liysy020/Automation_Temperature_Station/ESP32/Source Python/upload.py

import usocket as socket
import ssl
import json


def https_post(host, port, path, headers, data):
    addr_info = socket.getaddrinfo(host, port)[0][-1]
    sock = socket.socket()
    sock.settimeout(10) # 10 second timout for reads
    sock.connect(addr_info)
    sock = ssl.wrap_socket(sock, server_hostname=host)
    payload = json.dumps(data)
    payload_bytes = payload.encode('utf-8')
    header_lines = [
        f"Host: {host}",
        "Content-Type: application/json",
        "Connection: close",
    ]
    for k, v in headers.items():
        header_lines.append(f"{k}: {v}")
    header_lines.append(f"Content-Length: {len(payload_bytes)}")
    header_lines.append("")  # blank line
    request_lines = [
        f"POST {path} HTTP/1.1",
    ] + header_lines + [
       ""  # blank line separating headers and body
    ]
    request = "\r\n".join(request_lines).encode('utf-8') + payload_bytes
    sock.write(request)
    
    try:
        response = b""
        while True:
            line = sock.readline()
            if not line:
                break
            response += line
    except Exception as e:
        print("Socket timeout or error:", e)
    finally:
        sock.close()
    return response

def send (host, port, path, DEVICE_NAME, API_KEY, temp=0, humi=0):
    data = {
        "temperature": temp,
        "humidity": humi
    }
    headers = {
        "Device-Name": DEVICE_NAME,
        "Api-Key": API_KEY
    }
    return https_post(host, port, path, headers, data)
