liysy020/Automation_Temperature_Station/ESP32/Source Python/display_LCD1602.py

from machine import I2C, Pin
from lib.lcd_api import LcdApi
from lib.i2c_lcd import I2cLcd

class LCD_Display:
    def __init__(self, sda_pin, scl_pin):
        try:
            self.i2c = I2C(0, sda=Pin(sda_pin), scl=Pin(scl_pin), freq=100_000)
            devices = self.i2c.scan()
            self.lcd = I2cLcd(self.i2c, 0x27, 2, 16)
        except Exception as e:
            print("Invalid SDA or SCL pin:", e)
            self.lcd = None  # No LCD initialized due to pin error
        
    def display(self, line1, line2, backlight=True):
        if backlight:
            self.lcd.backlight_on()
        else:
            self.lcd.backlight_off()
        #display row 1
        self.lcd.move_to(0, 0)
        self.lcd.putstr (line1)
        #display row 2
        self.lcd.move_to(0, 1)
        self.lcd.putstr (line2)
